MostafaLotfy122/STM32-Smart-Lock/SMART LOCK CONTROLLER.kicad_sch

## KiCad design SMART LOCK CONTROLLER.kicad_sch (2026-06-03, last stored version)

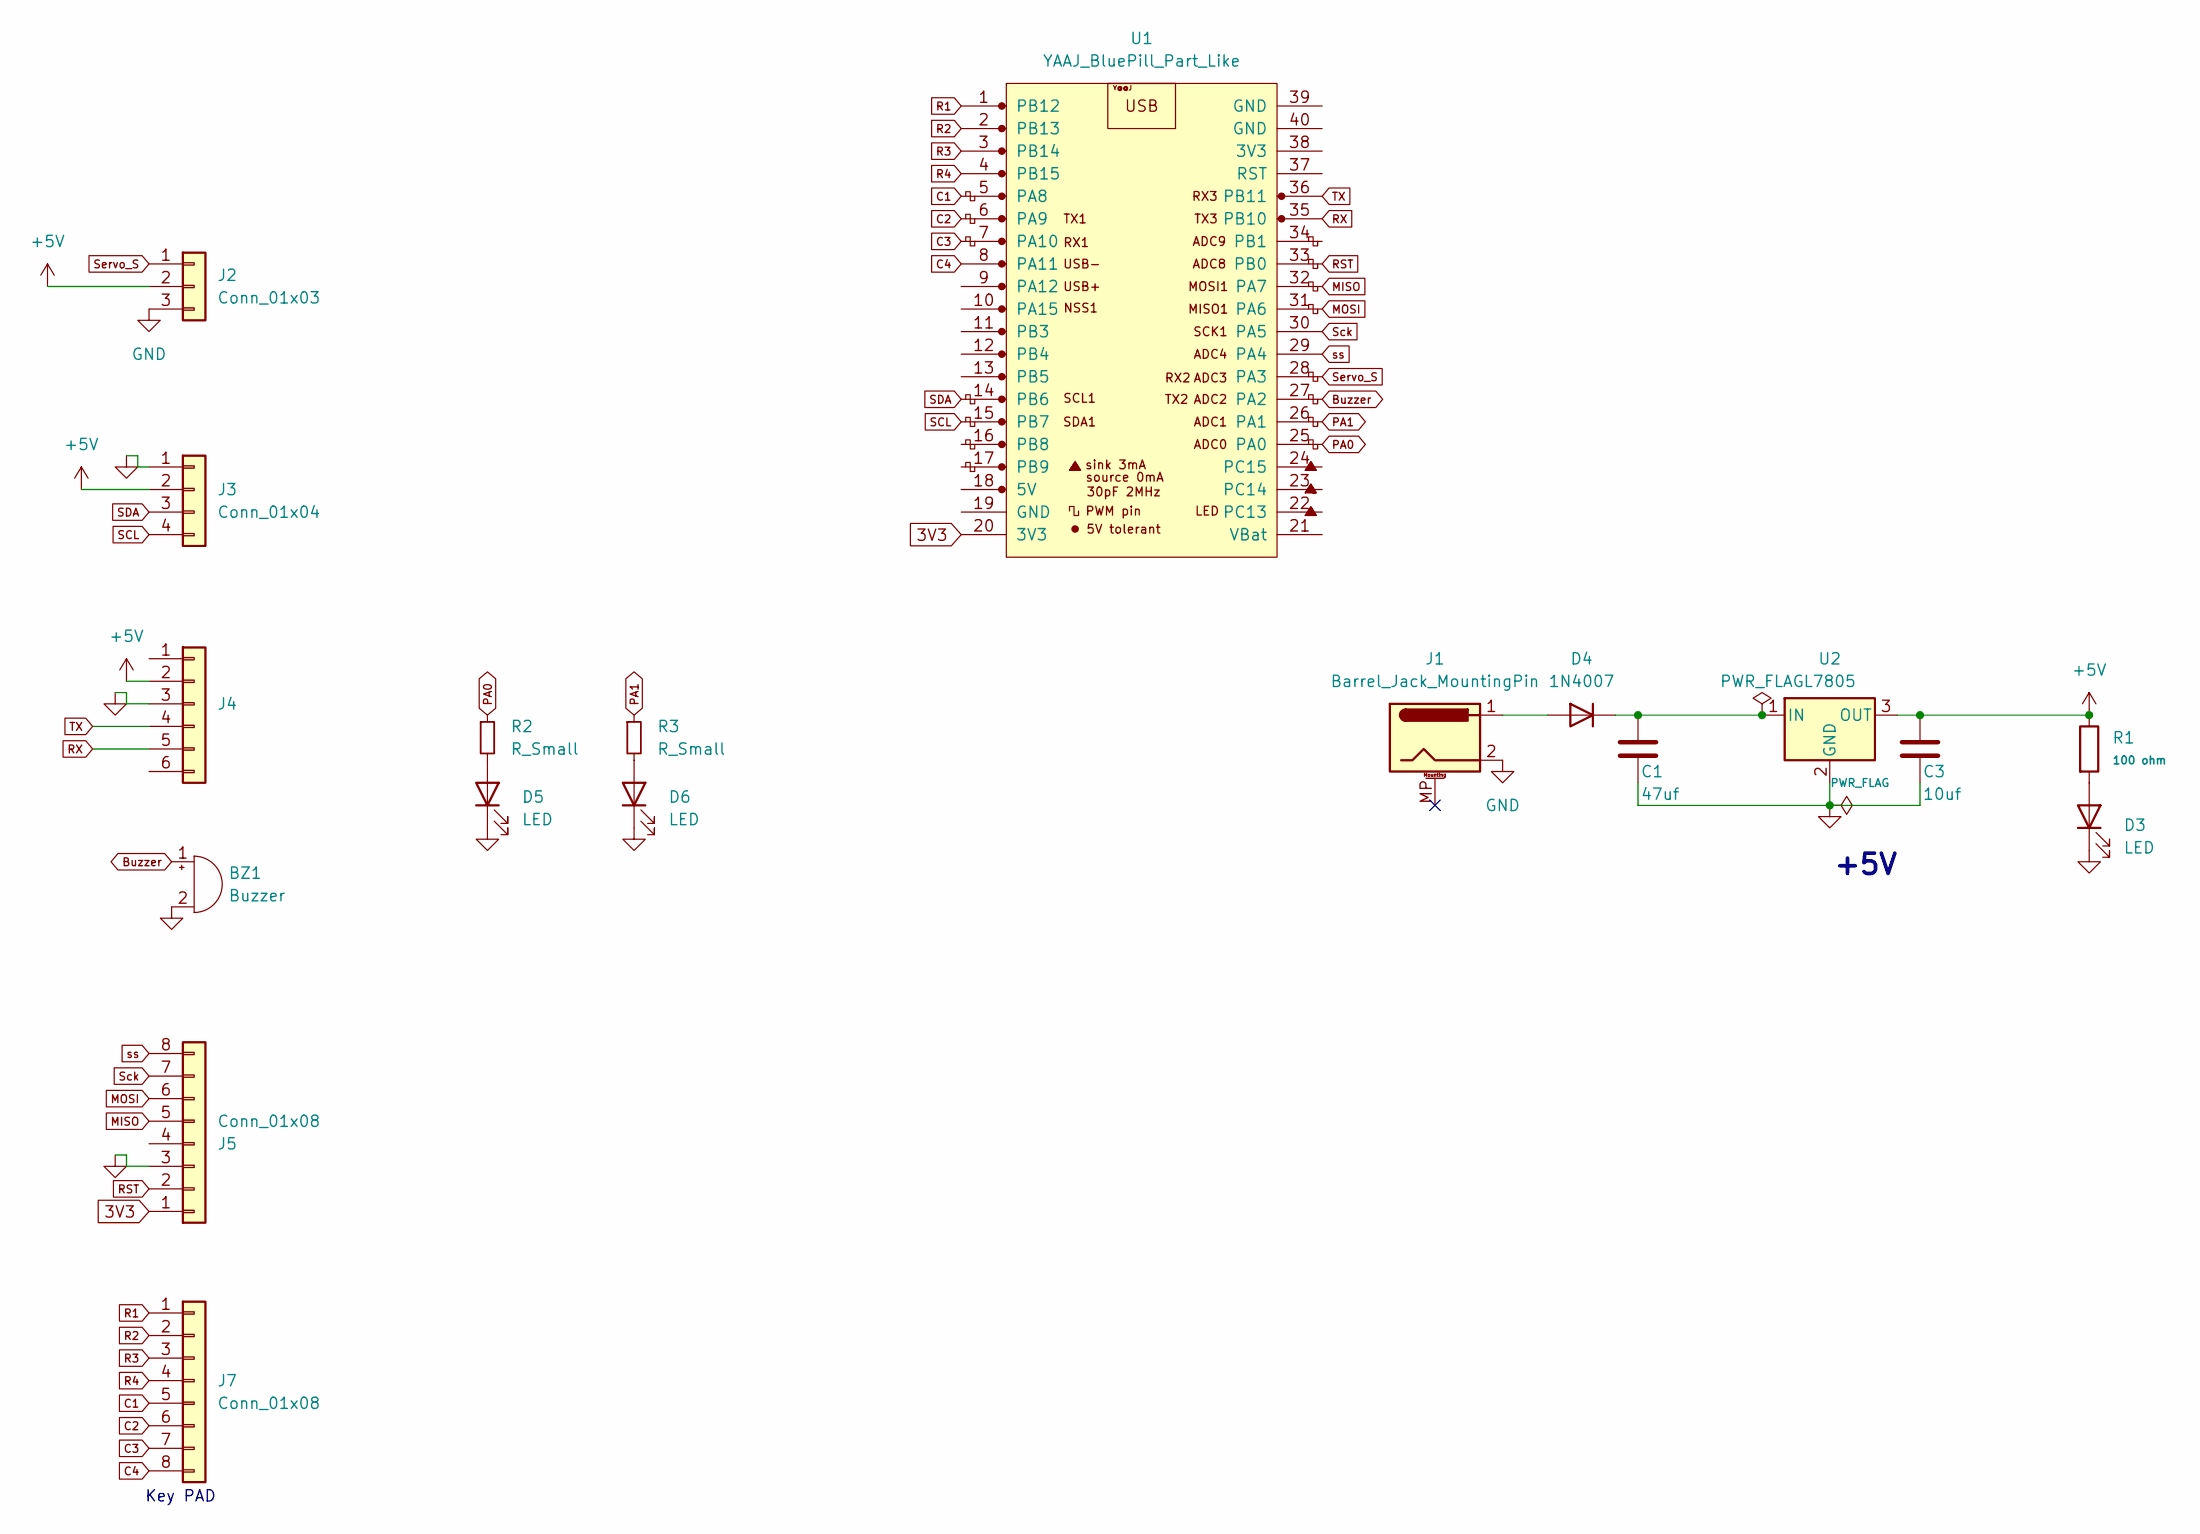
[picture p2: schematic SMART LOCK CONTROLLER.kicad_sch]

Parts:
BZ1: Buzzer; Buzzer_12x9.5RM7.6
C1: 47uf; C_Disc_D5.0mm_W2.5mm_P2.50mm
C3: 10uf; CP_Radial_D4.0mm_P2.00mm
D3: LED; LED_D3.0mm
D4: 1N4007; D_DO-41_SOD81_P10.16mm_Horizontal
D5, D6: LED; LED_D5.0mm
J1: Barrel_Jack_MountingPin; BarrelJack_Horizontal
J2: Conn_01x03; PinHeader_1x03_P2.54mm_Vertical
J3: Conn_01x04; PinHeader_1x04_P2.54mm_Vertical
J4: Conn_01x06; PinHeader_1x06_P2.54mm_Vertical
J5, J7: Conn_01x08; PinHeader_1x08_P2.54mm_Vertical
R1: 100 ohm; R_Axial_DIN0207_L6.3mm_D2.5mm_P7.62mm_Horizontal
R2, R3: R_Small; R_Axial_DIN0204_L3.6mm_D1.6mm_P7.62mm_Horizontal
U1: YAAJ_BluePill_Part_Like; YAAJ_BluePill_1
U2: L7805; TO-220-3_Vertical

Connections:
3V3: J5.1, U1.20 (3V3)
+5V: C3.1, J2.2, J3.2, J4.2, R1.1, U2.3 (OUT)
Buzzer: BZ1.1 (+), U1.27 (PA2)
C1: J7.5, U1.5 (PA8)
C2: J7.6, U1.6 (PA9)
C3: J7.7, U1.7 (PA10)
C4: J7.8, U1.8 (PA11)
GND: BZ1.2 (-), C1.2, C3.2, D3.1 (K), D5.1 (K), D6.1 (K), J1.2, J2.3, J3.1, J4.3, J5.3, U2.2 (GND)
MISO: J5.5, U1.32 (PA7)
MOSI: J5.6, U1.31 (PA6)
unnamed: C1.1, D4.1 (K), U2.1 (IN)
unnamed: D3.2 (A), R1.2
unnamed: D4.2 (A), J1.1
unnamed: D5.2 (A), R2.2
unnamed: D6.2 (A), R3.2
PA0: R2.1, U1.25 (PA0)
PA1: R3.1, U1.26 (PA1)
R1: J7.1, U1.1 (PB12)
R2: J7.2, U1.2 (PB13)
R3: J7.3, U1.3 (PB14)
R4: J7.4, U1.4 (PB15)
RST: J5.2, U1.33 (PB0)
RX: J4.5, U1.35 (PB10)
SCL: J3.4, U1.15 (PB7)
SDA: J3.3, U1.14 (PB6)
Sck: J5.7, U1.30 (PA5)
Servo_S: J2.1, U1.28 (PA3)
TX: J4.4, U1.36 (PB11)
ss: J5.8, U1.29 (PA4)

Notes on the sheet:
+5V
Key PAD
