MostafaLotfy122/STM32-Smart-Lock/Code/i2c-lcd.h

#ifndef I2C_LCD_H
#define I2C_LCD_H

#include "stm32f4xx_hal.h"

void lcd_init(void);
void lcd_send_string(char *str);
void lcd_put_cur(int row, int col);
void lcd_clear(void);
void lcd_send_data(char data);

#endif
